ac1ja/gc-1000-gps/docs/assembly/images/full_board.jpg

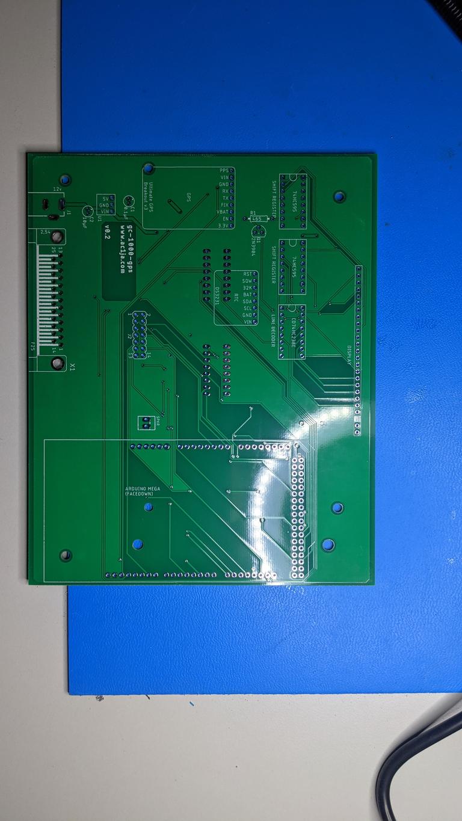
docs/assembly/images/full_board.jpg
