ac1ja/gc-1000-gps/docs/development/images/eagle_tutorial/describe_board_version.png

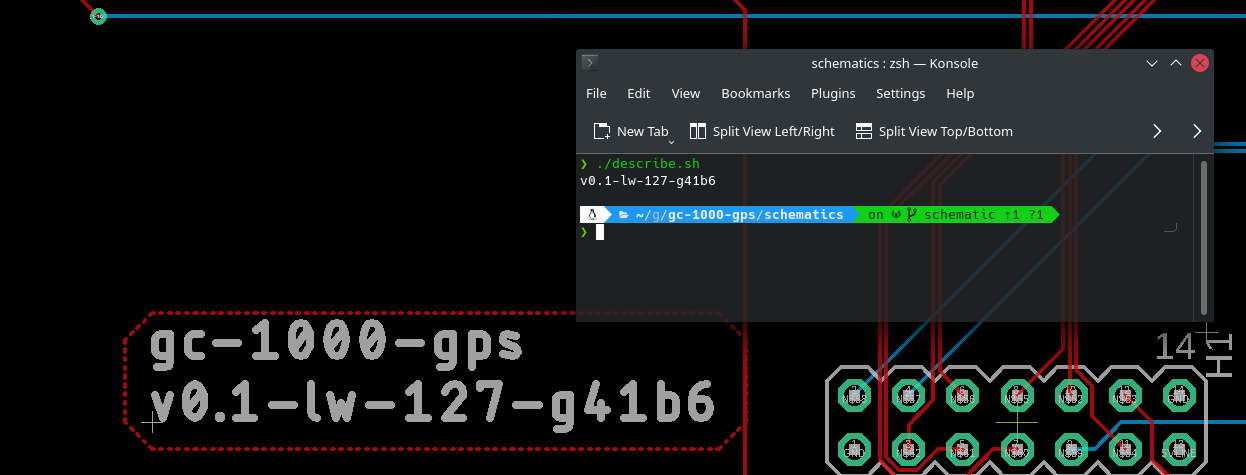
docs/development/images/eagle_tutorial/describe_board_version.png
