ac1ja/gc-1000-gps/docs/development/images/eagle_tutorial/load_job_file.png

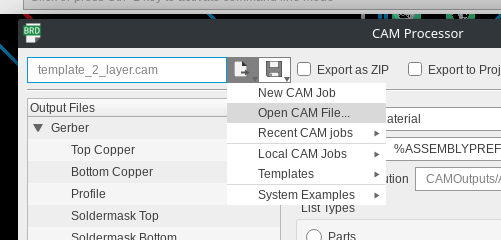
docs/development/images/eagle_tutorial/load_job_file.png
