ac1ja/gc-1000-gps/docs/development/images/eagle_tutorial/open_board.png

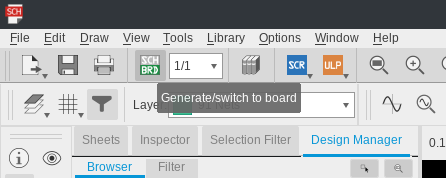
docs/development/images/eagle_tutorial/open_board.png
