ac1ja/gc-1000-gps/docs/development/images/eagle_tutorial/open_from_repo.png

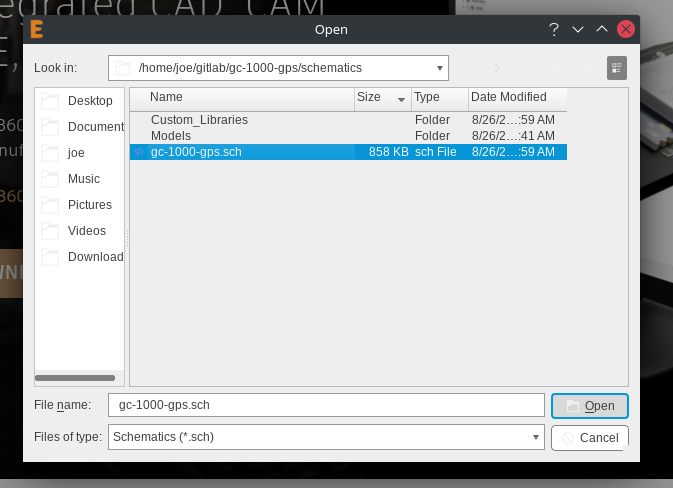
docs/development/images/eagle_tutorial/open_from_repo.png
