ac1ja/gc-1000-gps/docs/development/images/eagle_tutorial/select_cam.png

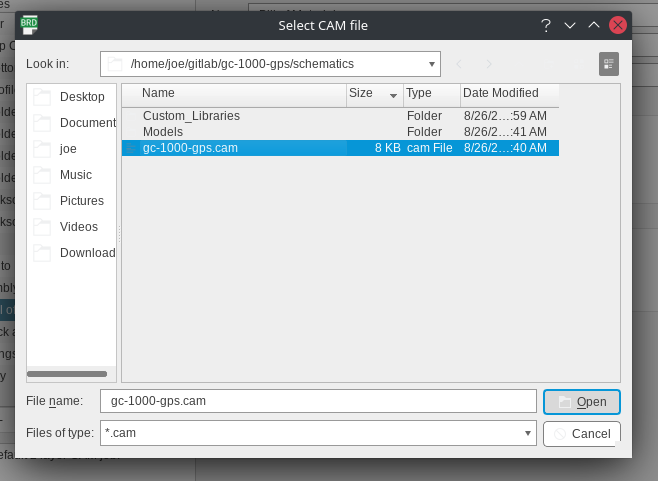
docs/development/images/eagle_tutorial/select_cam.png
