ac1ja/gc-1000-gps/firmware/build_flags.py

import subprocess

from datetime import date


today = date.today()

revision = (
    subprocess.check_output(
        [
            "git",
            "describe",
            "--abbrev=8",
            "--dirty",
            "--always",
            "--tags",
        ]
    )
    .strip()
    .decode("utf-8")
)

host = (
    subprocess.check_output(
        [
            "hostname",
        ]
    )
    .strip()
    .decode("utf-8")
)

username = (
    subprocess.check_output(
        [
            "id",
            "-u",
            "-n",
        ]
    )
    .strip()
    .decode("utf-8")
)

# Cleanup CI
if username == "root":
    username = "gitlab"
    host = "gitlab"

# Colors!
# revision = revision.replace("dirty", "\x1B[31mdirty\x1B[0m")
# host = "\x1B[34m" + host + "\x1B[0m"
# username = "\x1B[34m" + username + "\x1B[0m"


motd = f"\\r\\n\\r\\nStarting gc-1000-gps.\\r\\nThis software expects your terminal to be VT100 Compatable,\\r\\n\\r\\nUsing version {revision}.\\r\\ncompiled on {today.strftime('%B %d, %Y')} by {username} using {host}.\\r\\n\\r\\n"

print(f"-DMOTD='\"{motd}\"'")

# This is for the boardConfig
print("-I include/v2_Board")
